buddhi-rash/Smart-Cold-Chain-data-logger/Enclosure Design/part_files/boostpart.SLDPRT

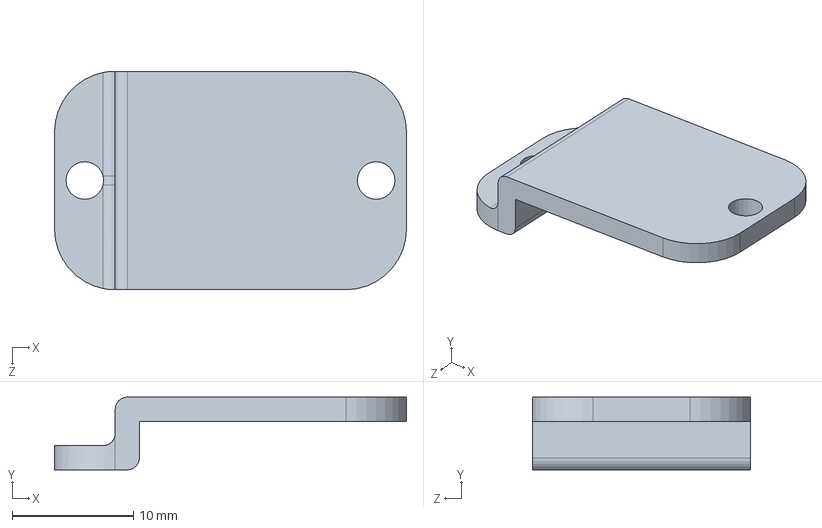
[picture p33: CAD file, 2026-08-17]
Enclosure Design/part_files/boostpart.SLDPRT
29.0 x 6.00 x 18.0 mm
