buddhi-rash/Smart-Cold-Chain-data-logger/Enclosure Design/part_files/acrylic_display.SLDPRT

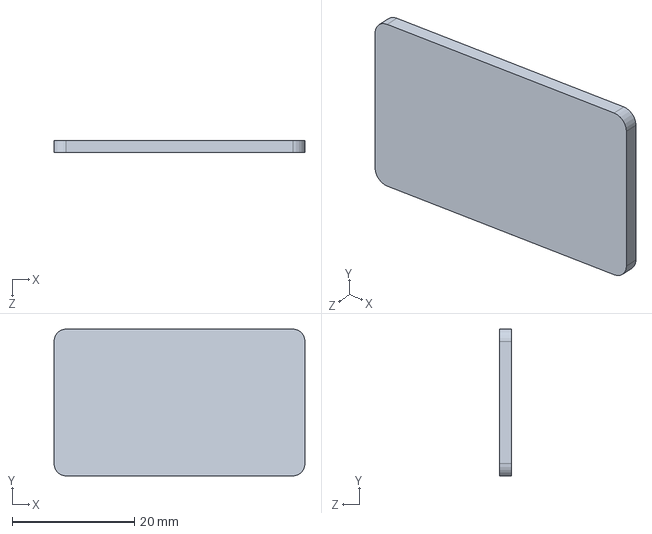
[picture p34: CAD file, 2026-08-17]
Enclosure Design/part_files/acrylic_display.SLDPRT
41.0 x 24.0 x 2.00 mm
