buddhi-rash/Smart-Cold-Chain-data-logger/Enclosure Design/part_files/switch_part_EDR.SLDPRT

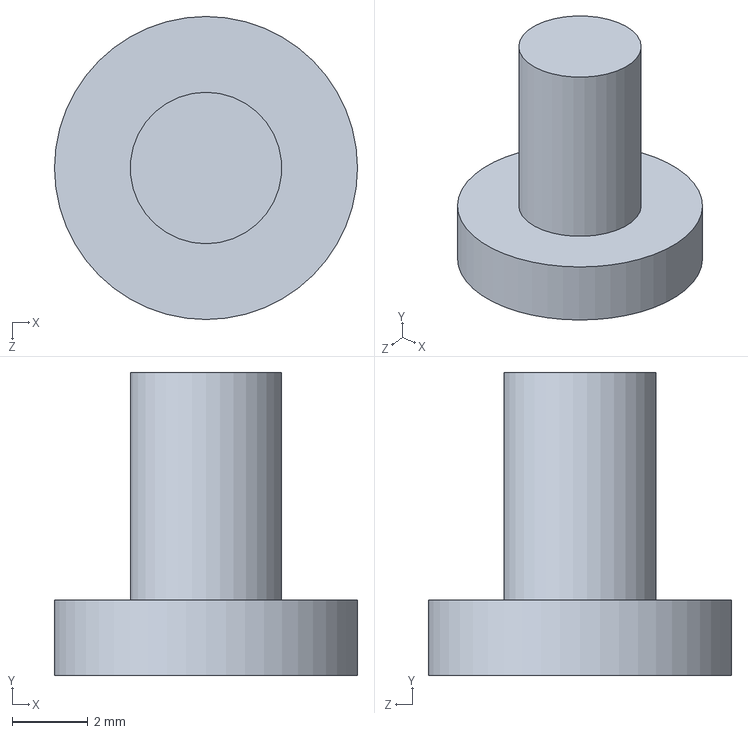
[picture p35: CAD file, 2026-08-17]
Enclosure Design/part_files/switch_part_EDR.SLDPRT
8.00 x 8.00 x 8.00 mm
